teguhprataman/thinkboard-lora-node/images/board-assembly-top-layer.PNG

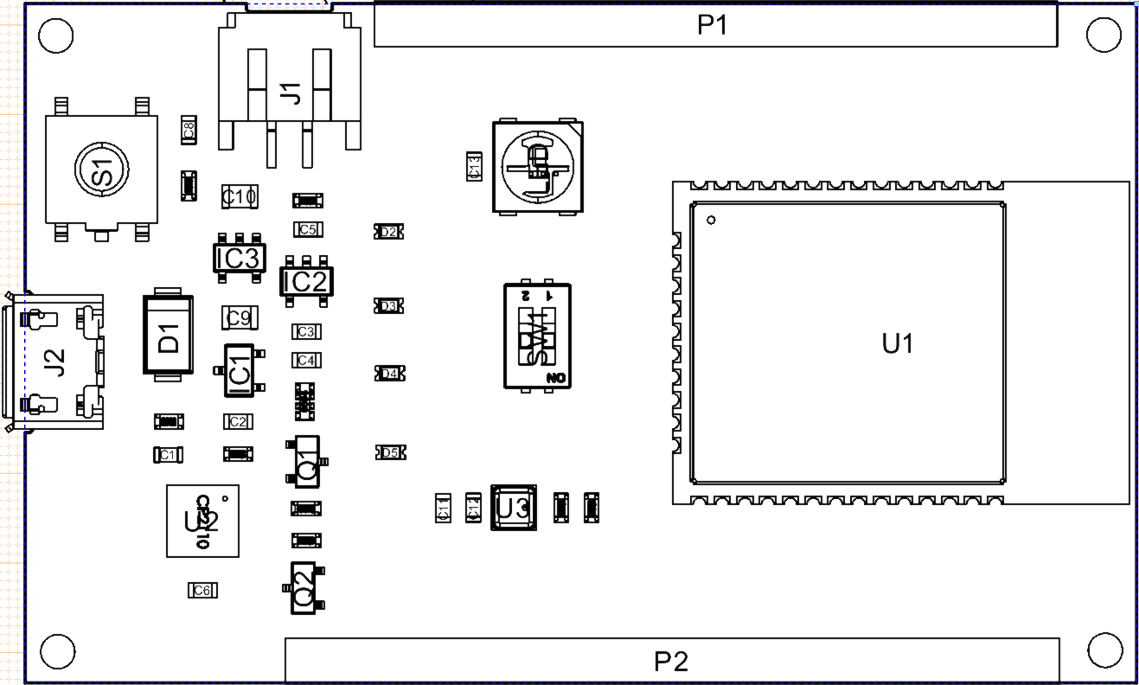
images/board-assembly-top-layer.PNG
